sam-was-here/PUMBA-Keyboard/PCB/keyboardPCBv2.kicad_sch

## KiCad design PCB/keyboardPCBv2.kicad_sch (2023-06-08)

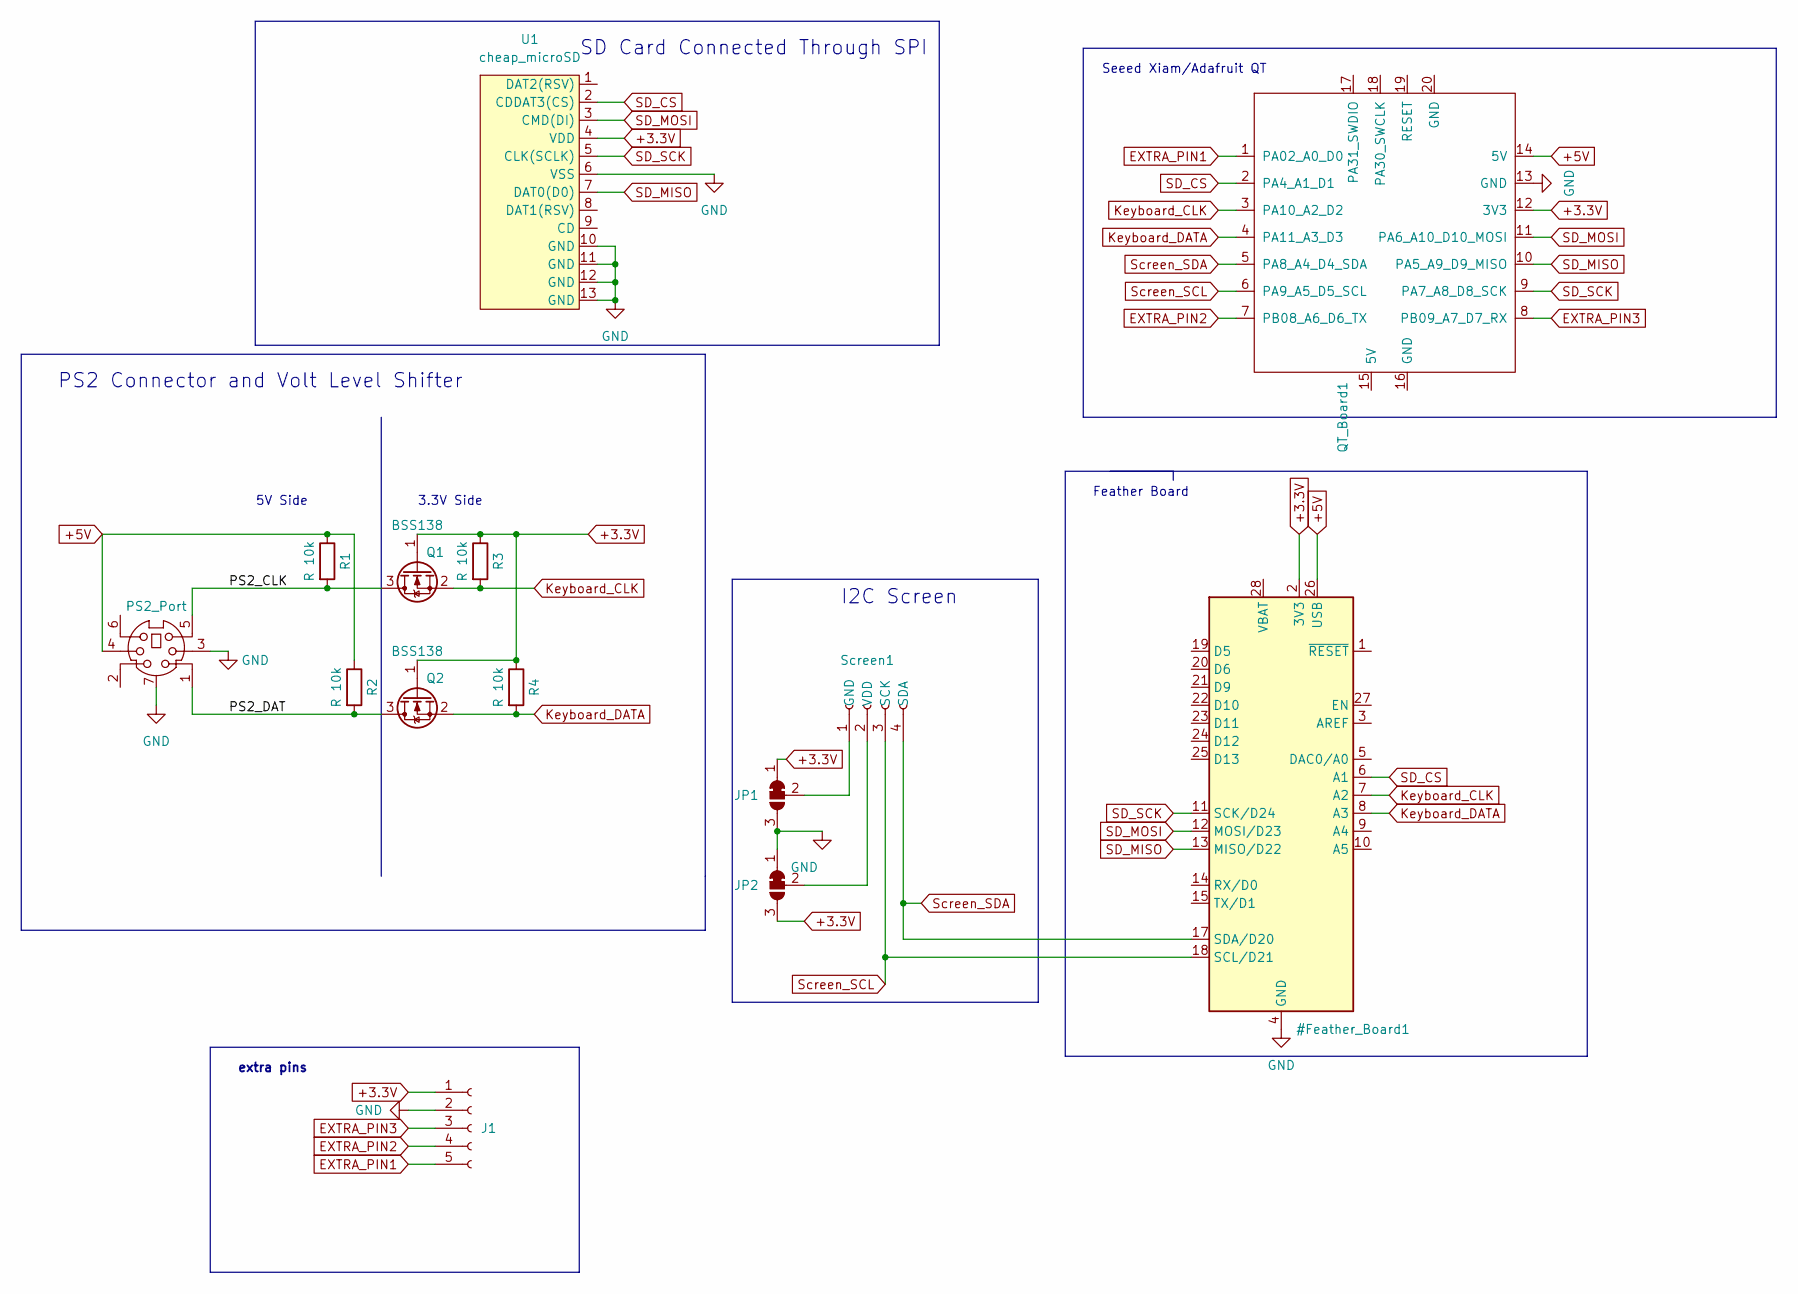
[picture p4: schematic keyboardPCBv2.kicad_sch]

Parts:
J1: Conn_01x05_Female; PinSocket_1x05_P2.54mm_Vertical
JP1, JP2: SolderJumper_3_Bridged12; SolderJumper-3_P1.3mm_Bridged12_RoundedPad1.0x1.5mm
P1: PS2_Port; Connector_Mini-DIN_Female_6Pin_2rows
Q1, Q2: BSS138; SOT-23; JLC SOT-23-3
QT_Board1: SeeeduinoXIAO; Seeeduino XIAO-MOUDLE14P-2.54-21X17.8MM
R1, R2, R3, R4: R 10k; R_0603_1608Metric_Pad0.98x0.95mm_HandSolder; JLC 0603
Screen1: Conn_01x04_Female; PinSocket_1x04_P2.54mm_Vertical
U1: cheap_microSD; CheapMicroSD; JLC TF-SMD_TF-15-15

Connections:
+3.3V: J1.1, J1.2, JP1.1 (A), JP1.3 (B), JP2.1 (A), JP2.3 (B), P1.3, P1.4, P1.7 (Shell), Q1.1 (G), Q1.2 (S), Q2.1 (G), Q2.2 (S), QT_Board1.2 (PA4_A1_D1), QT_Board1.3 (PA10_A2_D2), QT_Board1.4 (PA11_A3_D3), QT_Board1.5 (PA8_A4_D4_SDA), QT_Board1.6 (PA9_A5_D5_SCL), QT_Board1.9 (PA7_A8_D8_SCK), QT_Board1.10 (PA5_A9_D9_MISO), QT_Board1.11 (PA6_A10_D10_MOSI), QT_Board1.12 (3V3), QT_Board1.13 (GND), QT_Board1.14 (5V), R1.1, R2.1, R3.1, R3.2, R4.1, R4.2, Screen1.3 (SCK), Screen1.4 (SDA), U1.2 (CDDAT3(CS)), U1.3 (CMD(DI)), U1.4 (VDD), U1.5 (CLK(SCLK)), U1.6 (VSS), U1.7 (DAT0(D0)), U1.10 (GND), U1.11 (GND), U1.12 (GND), U1.13 (GND)
EXTRA_PIN1: J1.5, QT_Board1.1 (PA02_A0_D0)
EXTRA_PIN2: J1.4, QT_Board1.7 (PB08_A6_D6_TX)
EXTRA_PIN3: J1.3, QT_Board1.8 (PB09_A7_D7_RX)
unnamed: JP1.2 (C), Screen1.1 (GND)
unnamed: JP2.2 (C), Screen1.2 (VDD)
PS2_CLK: P1.5, Q1.3 (D), R1.2
PS2_DAT: P1.1, Q2.3 (D), R2.2

Notes on the sheet:
Feather Board
I2C Screen
5V Side
SD Card Connected Through SPI
3.3V Side
Seeed Xiam/Adafruit QT
PS2 Connector and Volt Level Shifter
extra pins
